galadam96/Simon-Reimagined/05_Documentation/IMG/1000015414.jpg

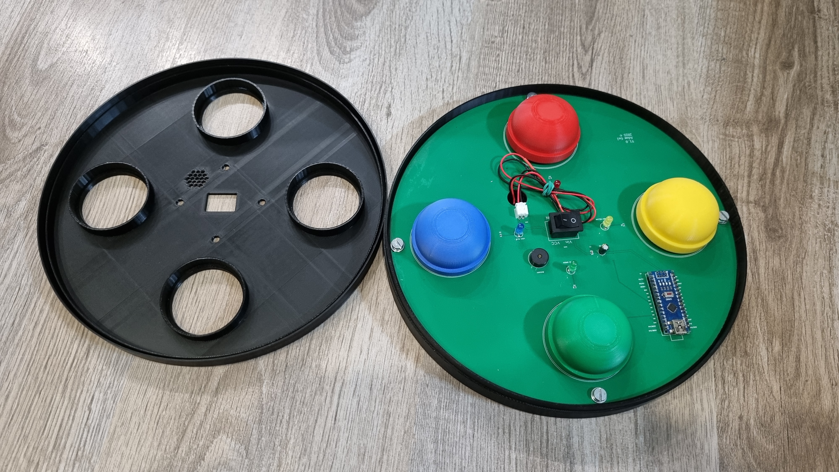
05_Documentation/IMG/1000015414.jpg
